mornepousse/Conchodytes/bringup/main/pmw3389_srom.c

/* SROM du PMW3389DM-T3QU — blob televerse a chaque demarrage.
 * Source : mrjohnk/PMW3389DM, Arduino Examples/PMW3389DM-polling/SROM.ino
 * 4094 octets. DIFFERENT de celui du PMW3360 (99,6 % des octets different) —
 * ne jamais intervertir les deux : c est le firmware de la puce.
 */
#include <stdint.h>

const unsigned short firmware_length = 4094;
const unsigned char firmware_data[] = {
    0x01, 0xE8, 0xBA, 0x26, 0x0B, 0xB2, 0xBE, 0xFE, 0x7E, 0x5F, 0x3C, 0xDB,
    0x15, 0xA8, 0xB3, 0xE4, 0x2B, 0xB5, 0xE8, 0x53, 0x07, 0x6D, 0x3B, 0xD1,
    0x20, 0xC2, 0x06, 0x6F, 0x3D, 0xD9, 0x11, 0xA0, 0xC2, 0xE7, 0x2D, 0xB9,
    0xD1, 0x20, 0xA3, 0xA5, 0xC8, 0xF3, 0x64, 0x4A, 0xF7, 0x4D, 0x18, 0x93,
    0xA4, 0xCA, 0xF7, 0x6C, 0x5A, 0x36, 0xEE, 0x5E, 0x3E, 0xFE, 0x7E, 0x7E,
    0x5F, 0x1D, 0x99, 0xB0, 0xC3, 0xE5, 0x29, 0xD3, 0x03, 0x65, 0x48, 0x12,
    0x87, 0x6D, 0x58, 0x32, 0xE6, 0x2F, 0xDC, 0x3A, 0xF2, 0x4F, 0xFD, 0x59,
    0x11, 0x81, 0x61, 0x21, 0xC0, 0x02, 0x86, 0x8E, 0x7F, 0x5D, 0x38, 0xF2,
    0x47, 0x0C, 0x7B, 0x55, 0x28, 0xB3, 0xE4, 0x4A, 0x16, 0xAB, 0xBF, 0xDD,
    0x38, 0xF2, 0x66, 0x4E, 0xFF, 0x5D, 0x19, 0x91, 0xA0, 0xA3, 0xA5, 0xC8,
    0x12, 0xA6, 0xAF, 0xDC, 0x3A, 0xD1, 0x41, 0x60, 0x75, 0x58, 0x24, 0x92,
    0xD4, 0x72, 0x6C, 0xE0, 0x2F, 0xFD, 0x23, 0x8D, 0x1C, 0x5B, 0xB2, 0x97,
    0x36, 0x3D, 0x0B, 0xA2, 0x49, 0xB1, 0x58, 0xF2, 0x1F, 0xC0, 0xCB, 0xF8,
    0x41, 0x4F, 0xCD, 0x1E, 0x6B, 0x39, 0xA7, 0x2B, 0xE9, 0x30, 0x16, 0x83,
    0xD2, 0x0E, 0x47, 0x8F, 0xE3, 0xB1, 0xDF, 0xA2, 0x15, 0xDB, 0x5D, 0x30,
    0xC5, 0x1A, 0xAB, 0x31, 0x99, 0xF3, 0xFA, 0xB2, 0x86, 0x69, 0xAD, 0x7A,
    0xE8, 0xA7, 0x18, 0x6A, 0xCC, 0xC8, 0x65, 0x23, 0x87, 0xA8, 0x5F, 0xF5,
    0x21, 0x59, 0x75, 0x09, 0x71, 0x45, 0x55, 0x25, 0x4B, 0xDA, 0xA1, 0xC3,
    0xF7, 0x41, 0xAB, 0x59, 0xD9, 0x74, 0x12, 0x55, 0x5F, 0xBC, 0xAF, 0xD9,
    0xFD, 0xB0, 0x1E, 0xA3, 0x0F, 0xFF, 0xDE, 0x11, 0x16, 0x6A, 0xAE, 0x0E,
    0xE1, 0x5D, 0x3C, 0x10, 0x43, 0x9A, 0xA1, 0x0B, 0x24, 0x8F, 0x0D, 0x7F,
    0x0B, 0x5E, 0x4C, 0x42, 0xA4, 0x84, 0x2C, 0x40, 0xD0, 0x55, 0x39, 0xE6,
    0x4B, 0xF8, 0x9B, 0x2F, 0xDC, 0x28, 0xFF, 0xFA, 0xB5, 0x85, 0x19, 0xE5,
    0x28, 0xA1, 0x77, 0xAA, 0x73, 0xF3, 0x03, 0xC7, 0x62, 0xA6, 0x91, 0x18,
    0xC9, 0xB0, 0xCD, 0x05, 0xDC, 0xCA, 0x81, 0x26, 0x1A, 0x47, 0x40, 0xDA,
    0x36, 0x7D, 0x6A, 0x53, 0xC8, 0x5A, 0x77, 0x5D, 0x19, 0xA4, 0x1B, 0x23,
    0x83, 0xD0, 0xB2, 0xAA, 0x0E, 0xBF, 0x77, 0x4E, 0x3A, 0x3B, 0x59, 0x00,
    0x31, 0x0D, 0x02, 0x1B, 0x88, 0x7A, 0xD4, 0xBD, 0x9D, 0xCC, 0x58, 0x04,
    0x69, 0xF6, 0x3B, 0xCA, 0x42, 0xE2, 0xFD, 0xC3, 0x3D, 0x39, 0xC5, 0xD0,
    0x71, 0xE4, 0xC8, 0xB7, 0x3E, 0x3F, 0xC8, 0xE9, 0xCA, 0xC9, 0x3F, 0x04,
    0x4E, 0x1B, 0x79, 0xCA, 0xA5, 0x61, 0xC2, 0xED, 0x1D, 0xA6, 0xDA, 0x5A,
    0xE9, 0x7F, 0x65, 0x8C, 0xBE, 0x12, 0x6E, 0xA4, 0x5B, 0x33, 0x2F, 0x84,
    0x28, 0x9C, 0x1C, 0x88, 0x2D, 0xFF, 0x07, 0xBF, 0xA6, 0xD7, 0x5A, 0x88,
    0x86, 0xB0, 0x3F, 0xF6, 0x31, 0x5B, 0x11, 0x6D, 0xF5, 0x58, 0xEB, 0x58,
    0x02, 0x9E, 0xB5, 0x9A, 0xB1, 0xFF, 0x25, 0x9D, 0x8B, 0x4F, 0xB6, 0x0A,
    0xF9, 0xEA, 0x3E, 0x3F, 0x21, 0x09, 0x65, 0x21, 0x22, 0xFE, 0x3D, 0x4E,
    0x11, 0x5B, 0x9E, 0x5A, 0x59, 0x8B, 0xDD, 0xD8, 0xCE, 0xD6, 0xD9, 0x59,
    0xD2, 0x1E, 0xFD, 0xEF, 0x0D, 0x1B, 0xD9, 0x61, 0x7F, 0xD7, 0x2D, 0xAD,
    0x62, 0x09, 0xE5, 0x22, 0x63, 0xEA, 0xC7, 0x31, 0xD9, 0xA1, 0x38, 0x80,
    0x5C, 0xA7, 0x32, 0x82, 0xEC, 0x1B, 0xA2, 0x49, 0x5A, 0x06, 0xD2, 0x7C,
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
};
